thingSoC/TSOC_GROVEY_ONE/TSOC_GROVEY_ONE/documentation/pinout/TSOC_GROVEY_ONE_pinout.pdf

Sheet1

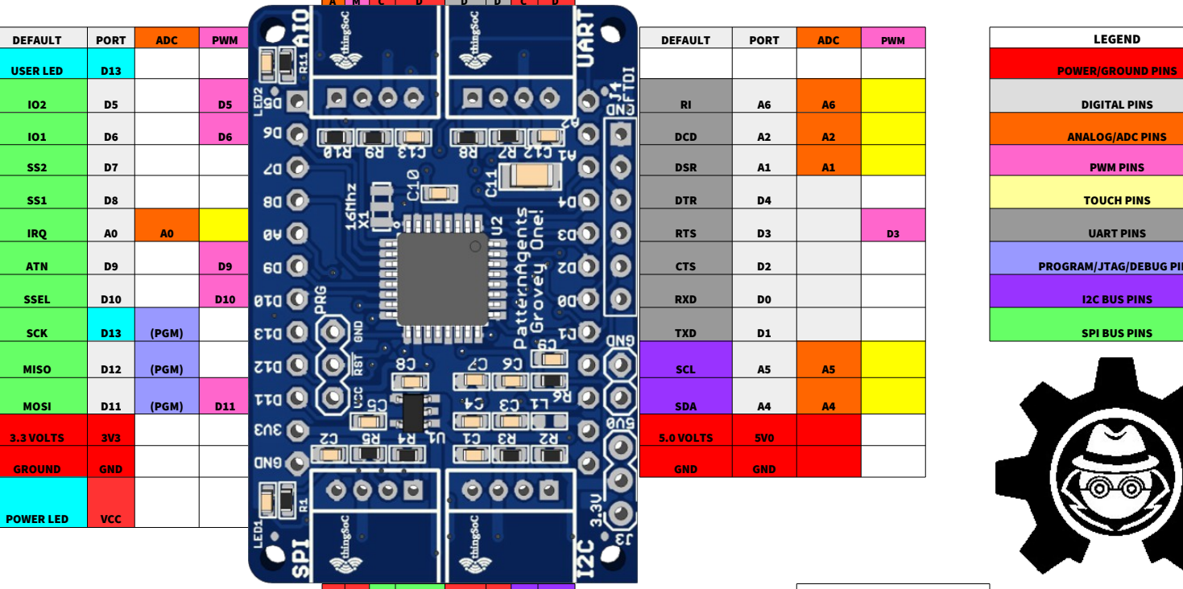
[picture p3: figure]
USER LED; POWER/GROUND PINS; DIGITAL PINS; DCD; ANALOG/ADC PINS; DSR; PWM PINS; DTR; TOUCH PINS; IRQ; RTS; UART PINS; SSEL; RXD; I2C BUS PINS; SCK; (PGM); TXD; SPI BUS PINS; MISO; SCL; MOSI; SDA; 3.3 VOLTS; 5.0 VOLTS; GROUND; GND; POWER LED; VCC

Page 1

DEFAULT | PORT | ADC | PWM | DEFAULT | PORT | ADC | PWM | LEGEND
ATN | D9 | D9 | CTS | D2 | PROGRAM/JTAG/DEBUG PINS

## PatternAgents

TSOC_GROVEY_ONE

A 3 | D 5 | P W R | G N D | D 0 | D 1 | P W R | G N D
A N A | P W M | V C C | G N D | R X D | T X D | V C C | G N D

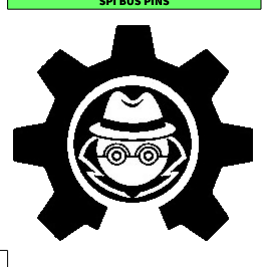
[picture p4: figure]

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
### 5 http://github.com/thingsoc/
