thingSoC/TSOC_GROVEY_ONE/TSOC_GROVEY_ONE/documentation/pinout/TSOC_GROVEY_ONE_pinout.jpg

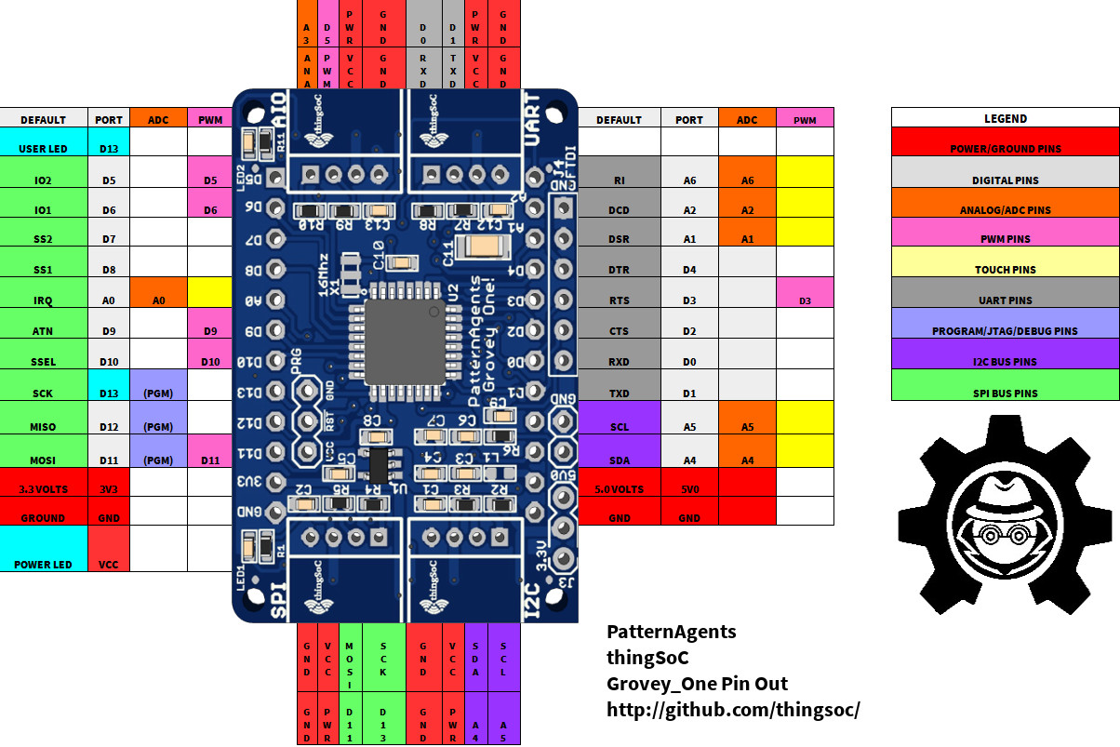
TSOC_GROVEY_ONE/documentation/pinout/TSOC_GROVEY_ONE_pinout.jpg
