thingSoC/TSOC_GROVEY_ONE/TSOC_GROVEY_ONE/eagleUp/eagleUp_TSOC_GROVEY_ONE_board_bottom.jpg

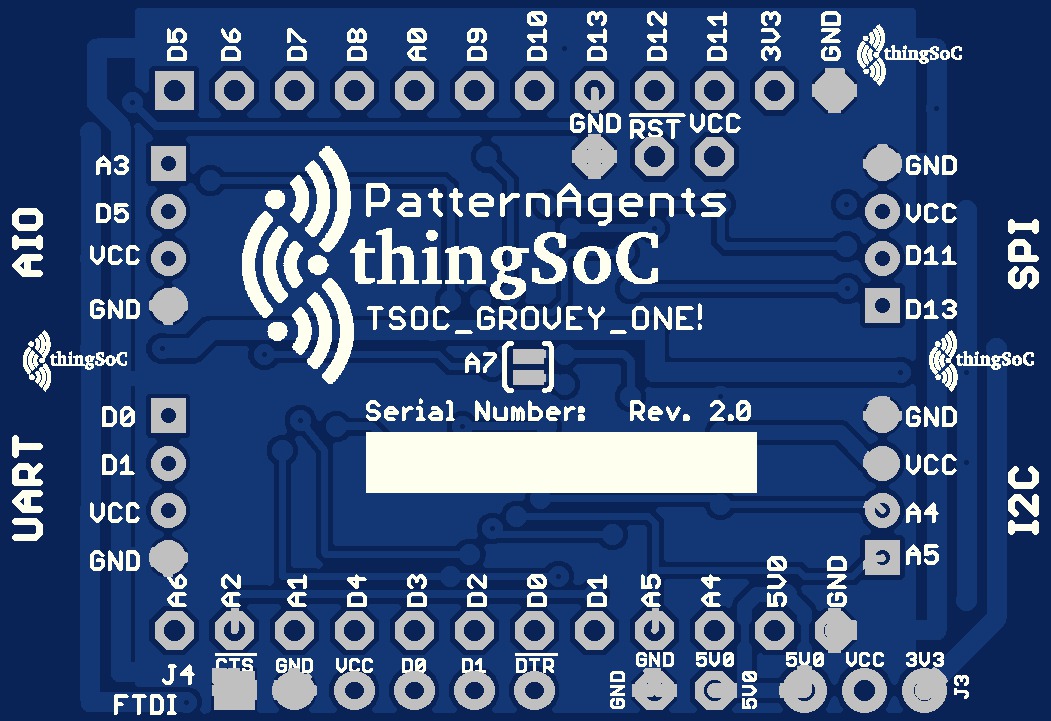
TSOC_GROVEY_ONE/eagleUp/eagleUp_TSOC_GROVEY_ONE_board_bottom.jpg
