thingSoC/TSOC_GROVEY_ONE/TSOC_GROVEY_ONE/images/product/TSOC_GROVEY_ONE_pop_top.png

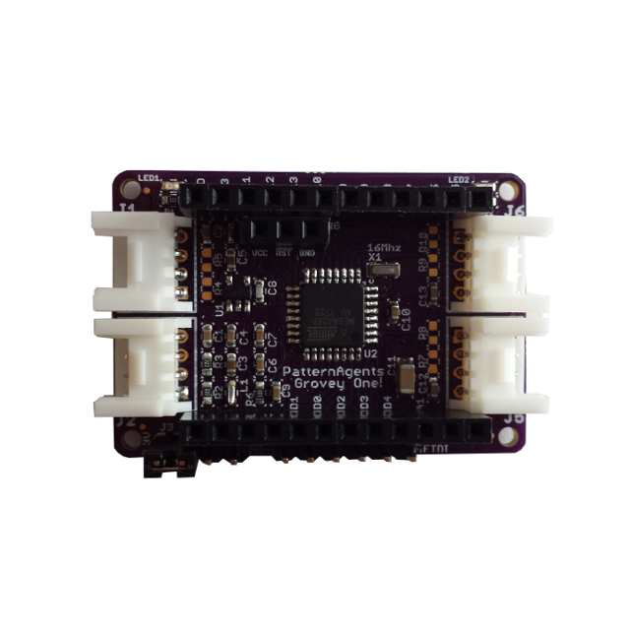
TSOC_GROVEY_ONE/images/product/TSOC_GROVEY_ONE_pop_top.png
