thingSoC/TSOC_GROVEY_ONE/TSOC_GROVEY_ONE/images/product/TSOC_GROVEY_ONE_top_pop.png

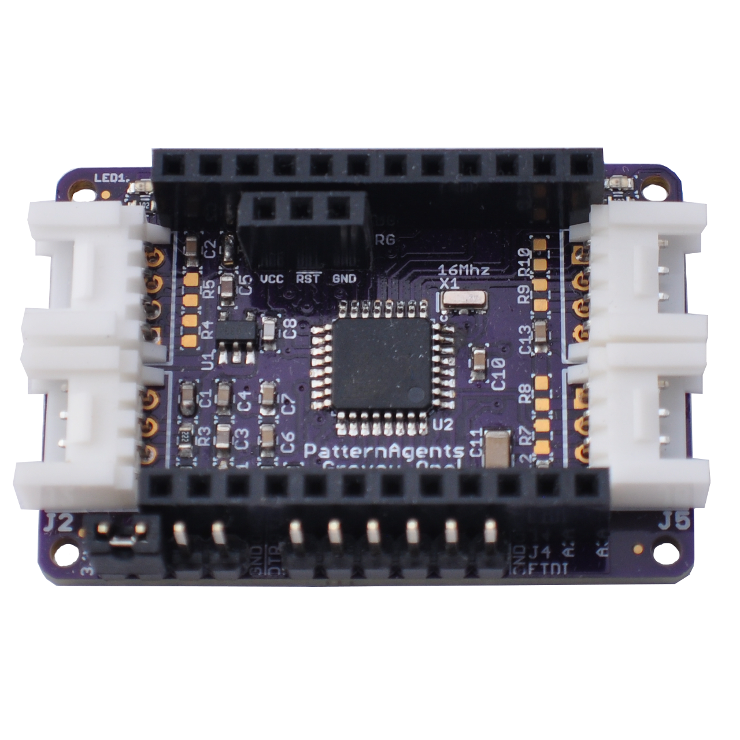
TSOC_GROVEY_ONE/images/product/TSOC_GROVEY_ONE_top_pop.png
