thingSoC/TSOC_GROVEY_ONE/TSOC_GROVEY_ONE/images/product/TSOC_GROVEY_ONE_with_FTDI_long.jpg

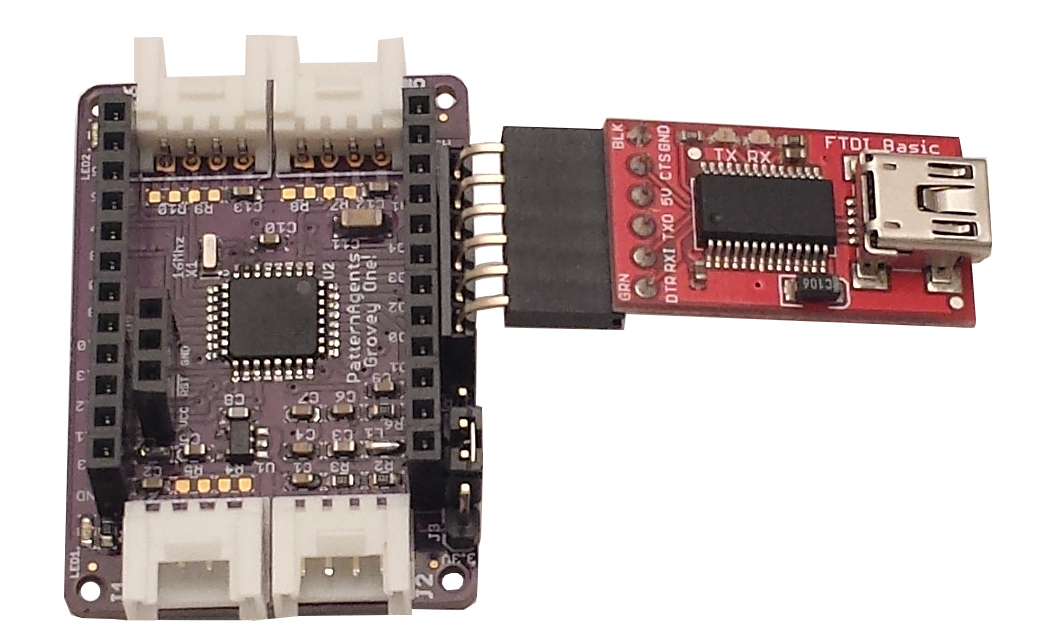
TSOC_GROVEY_ONE/images/product/TSOC_GROVEY_ONE_with_FTDI_long.jpg
