thingSoC/TSOC_GROVEY_ONE/TSOC_GROVEY_ONE/images/product/TSOC_GROVEY_ONE_with_programmer.jpg

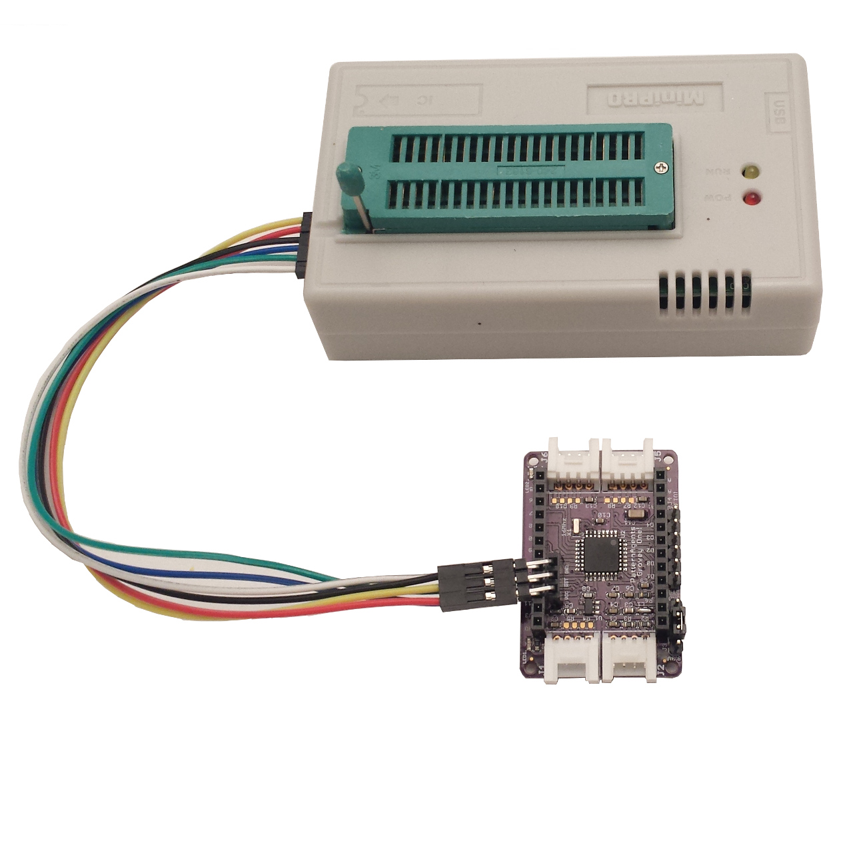
TSOC_GROVEY_ONE/images/product/TSOC_GROVEY_ONE_with_programmer.jpg
