thingSoC/TSOC_GROVEY_ONE/TSOC_GROVEY_ONE/images/raw/20160921_100233.jpg

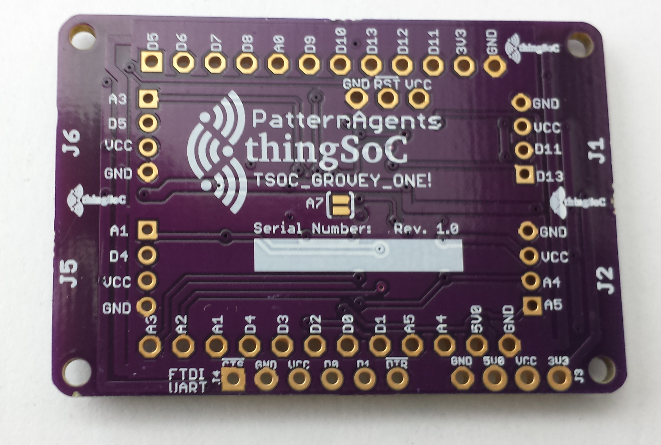
TSOC_GROVEY_ONE/images/raw/20160921_100233.jpg
