thingSoC/TSOC_GROVEY_ONE/TSOC_GROVEY_ONE/images/raw/20160928_184255.jpg

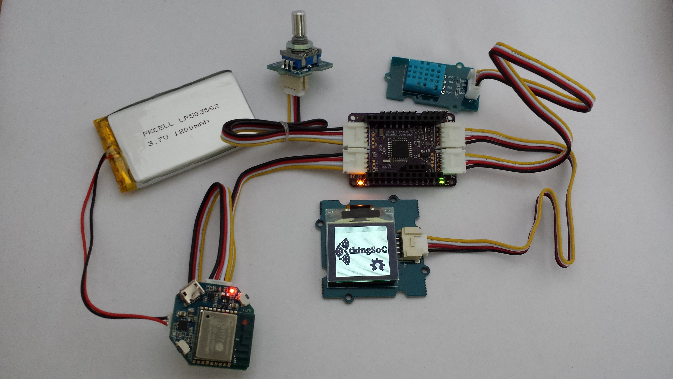
TSOC_GROVEY_ONE/images/raw/20160928_184255.jpg
