thingSoC/TSOC_GROVEY_ONE/TSOC_GROVEY_ONE/images/raw/20160929_131808.jpg

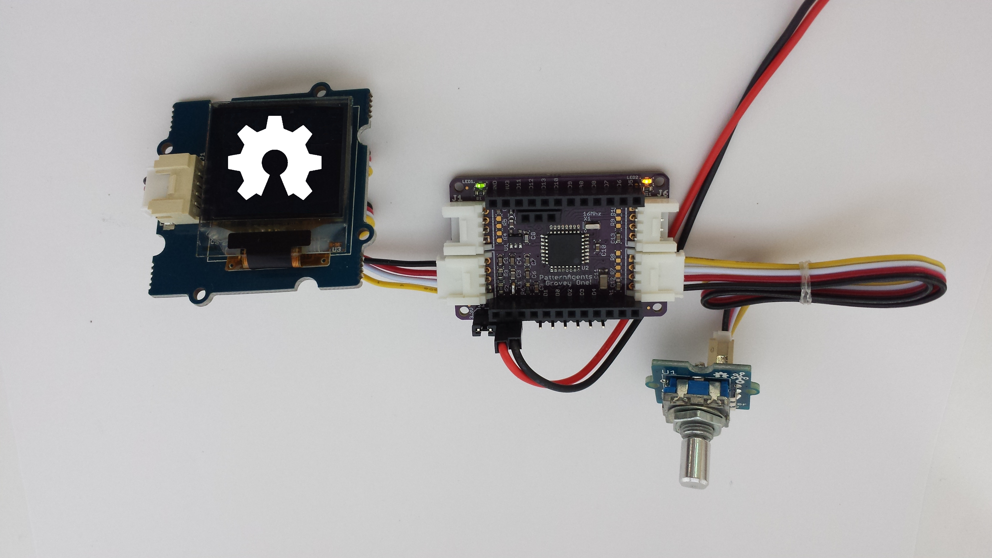
TSOC_GROVEY_ONE/images/raw/20160929_131808.jpg
