thingSoC/TSOC_GROVEY_ONE/TSOC_GROVEY_ONE/images/raw/20160929_132144.jpg

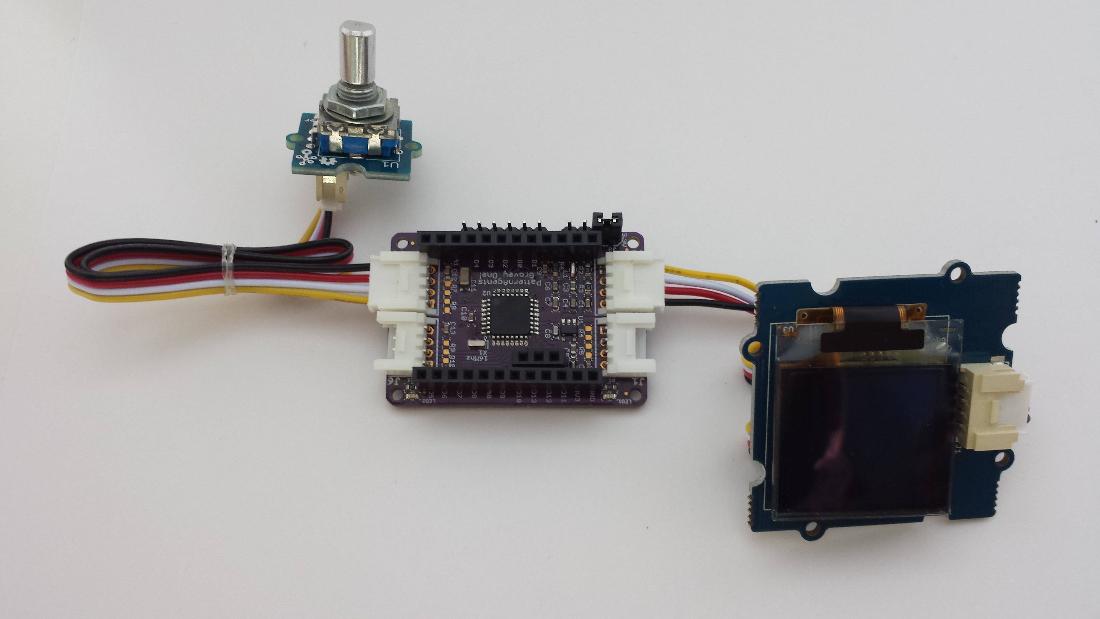
TSOC_GROVEY_ONE/images/raw/20160929_132144.jpg
