thingSoC/TSOC_GROVEY_ONE/TSOC_GROVEY_ONE/revisions/R1_0/TSOC_GROVEY_ONE_iso.png

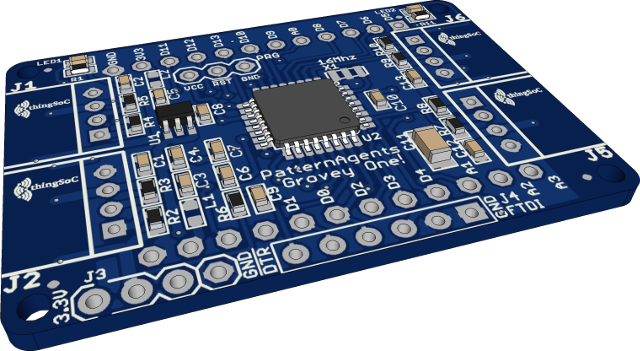
TSOC_GROVEY_ONE/revisions/R1_0/TSOC_GROVEY_ONE_iso.png
