thingSoC/TSOC_GROVEY_ONE/TSOC_GROVEY_ONE/revisions/R1_0/TSOC_GROVEY_ONE_top.png

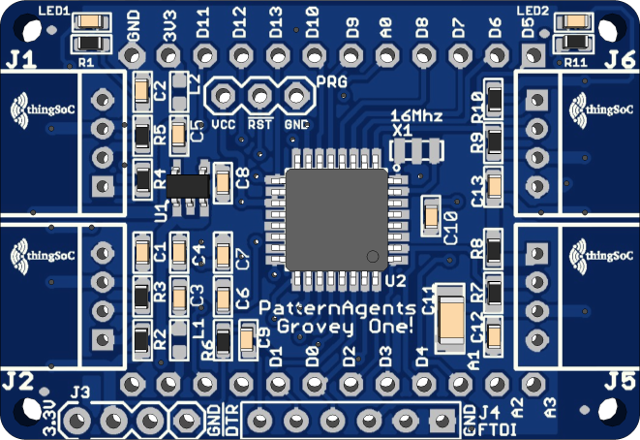
TSOC_GROVEY_ONE/revisions/R1_0/TSOC_GROVEY_ONE_top.png
