thingSoC/TSOC_GROVEY_ONE/TSOC_GROVEY_ONE/hardware/TSOC_GROVEY_ONE_sch.pdf

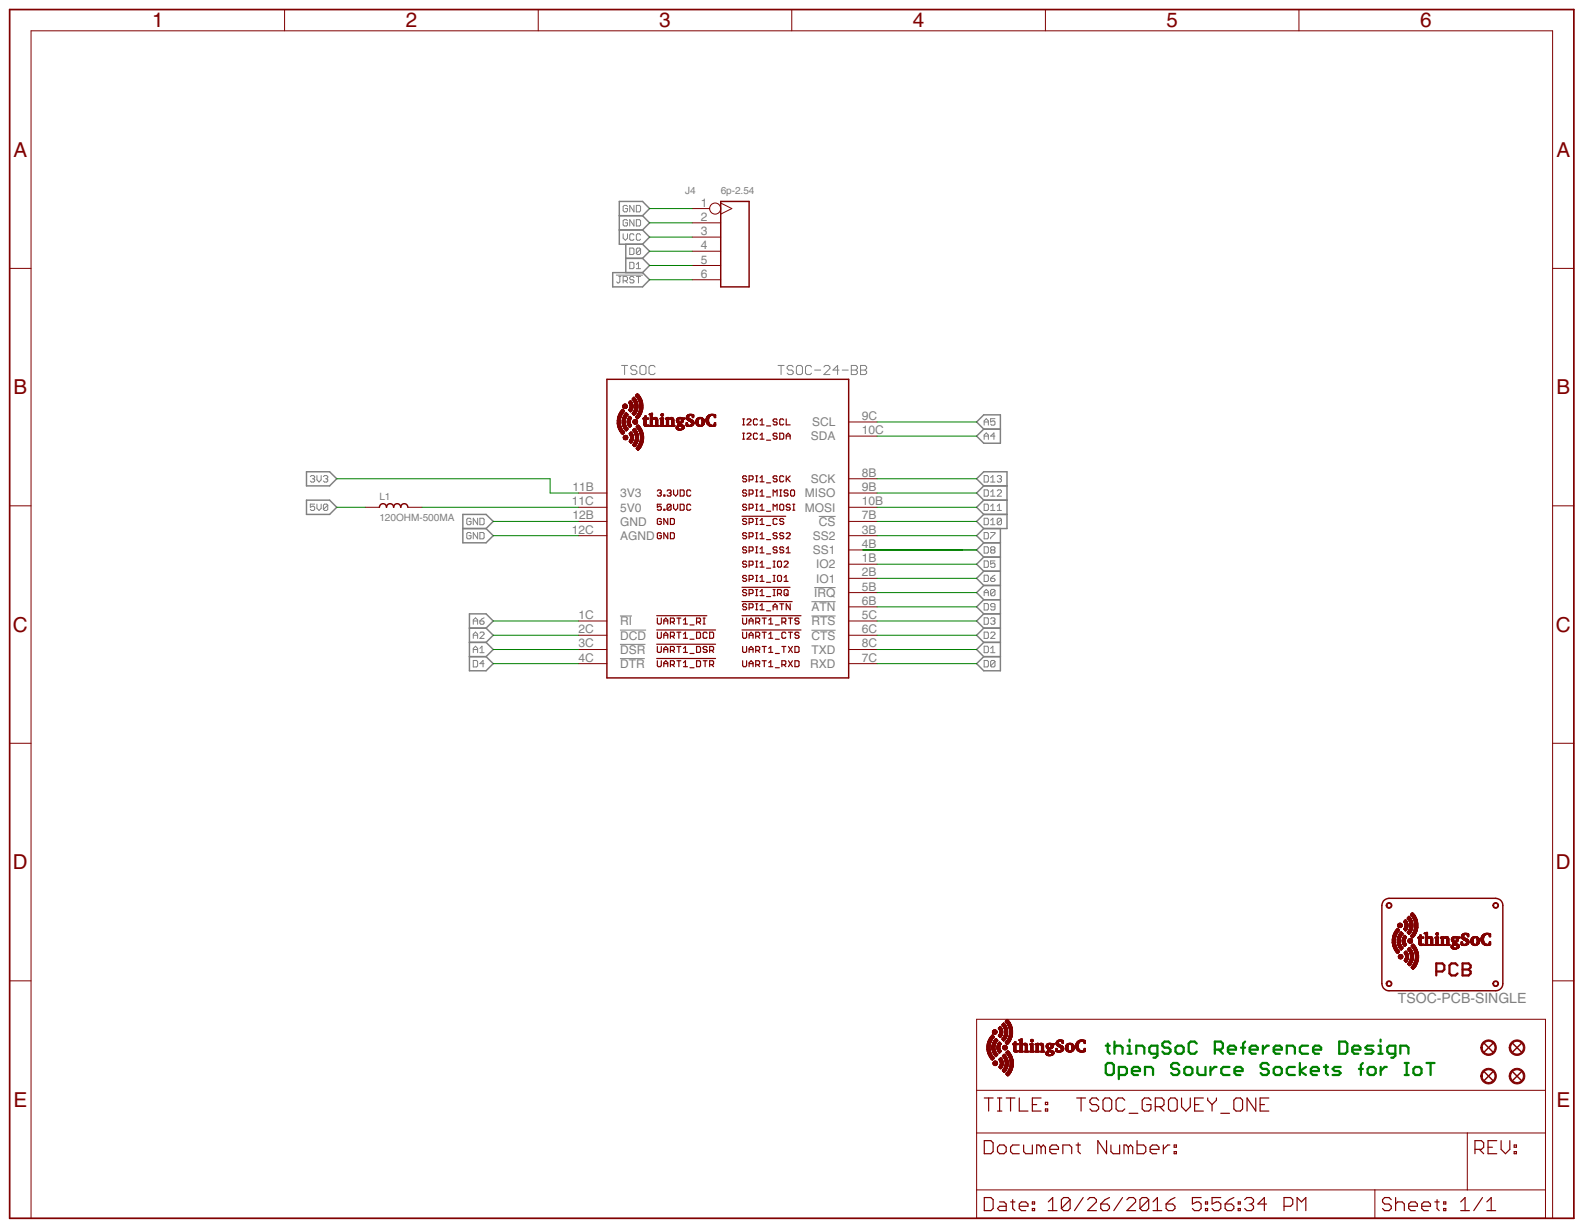
[picture p48: page 1]

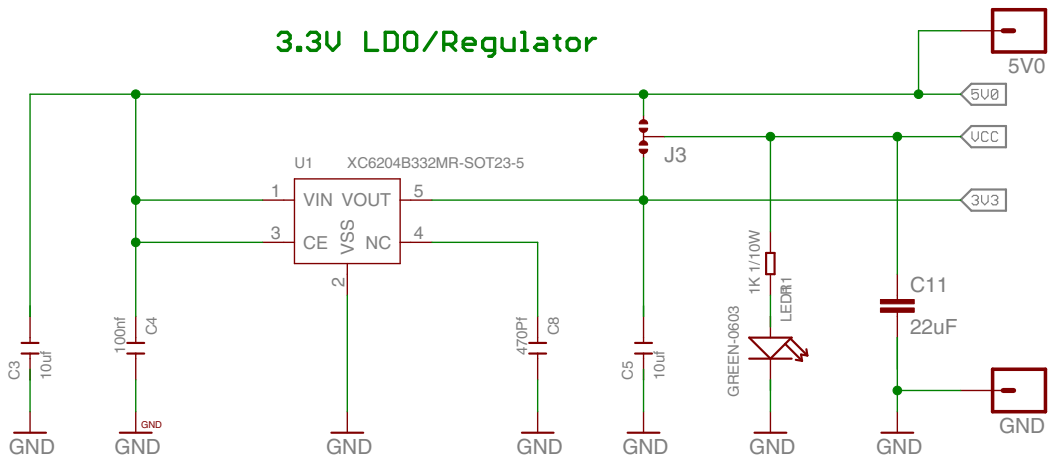
[picture p49: page 2]

100nf GND GND GND GND

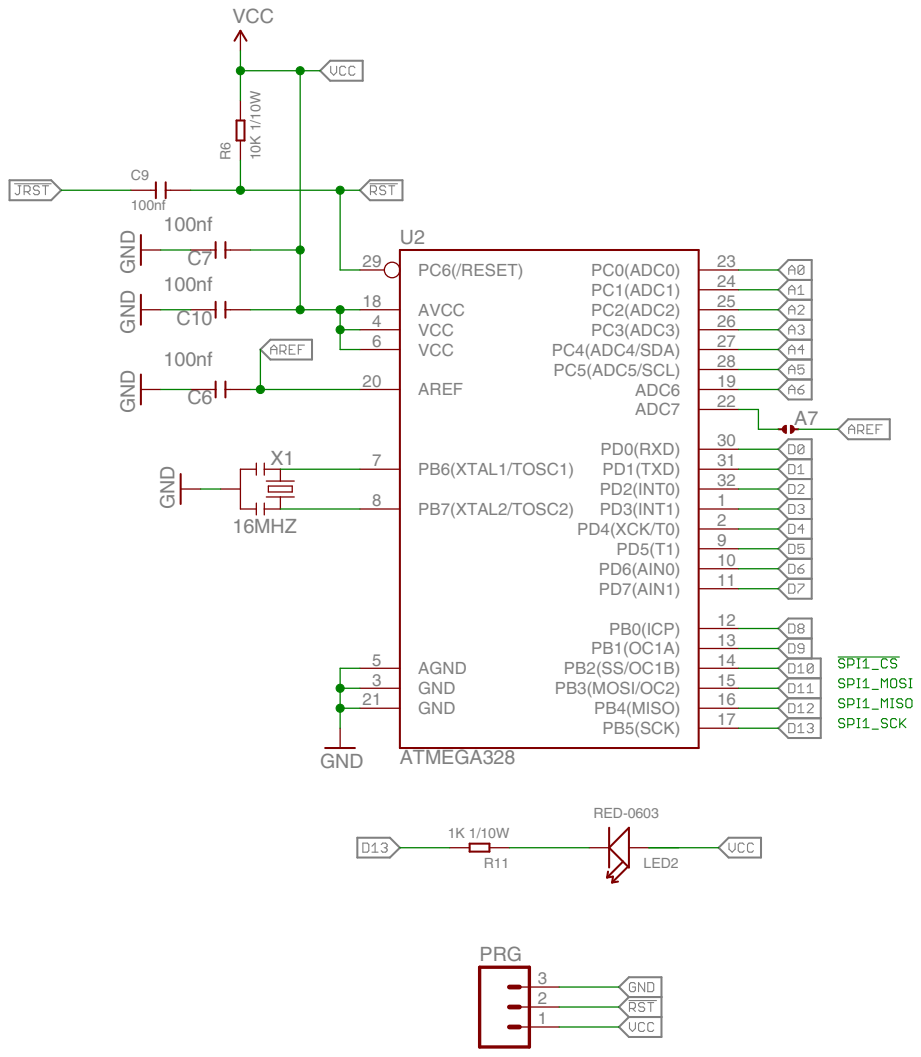
[picture p50: page 3]

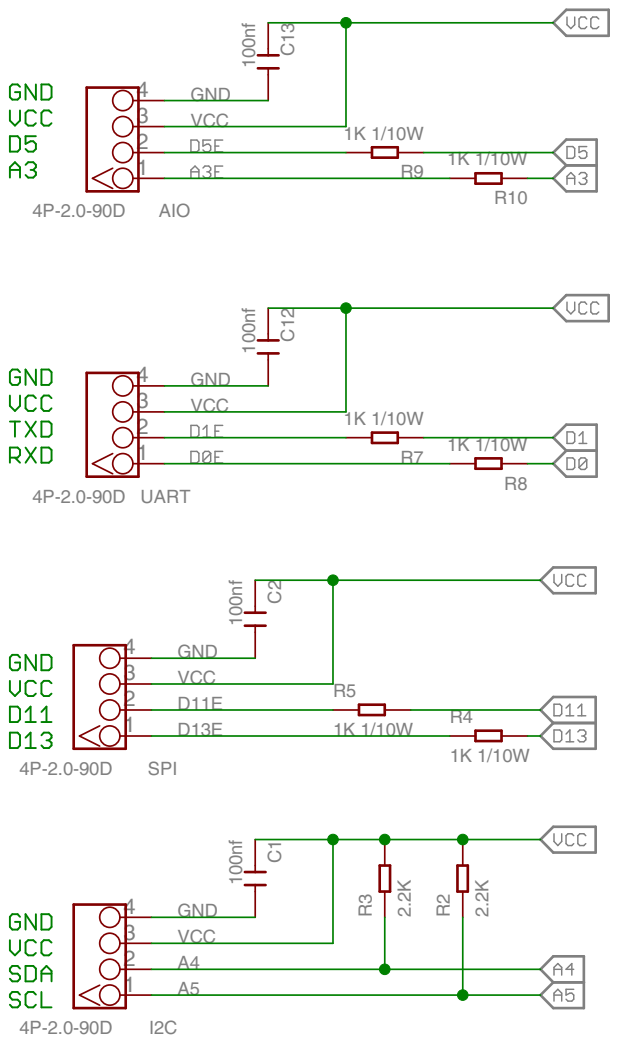
[picture p51: page 4]
