thingSoC/TSOC_GROVEY_ONE/TSOC_GROVEY_ONE/hardware/TSOC_GROVEY_ONE_sch_black.pdf

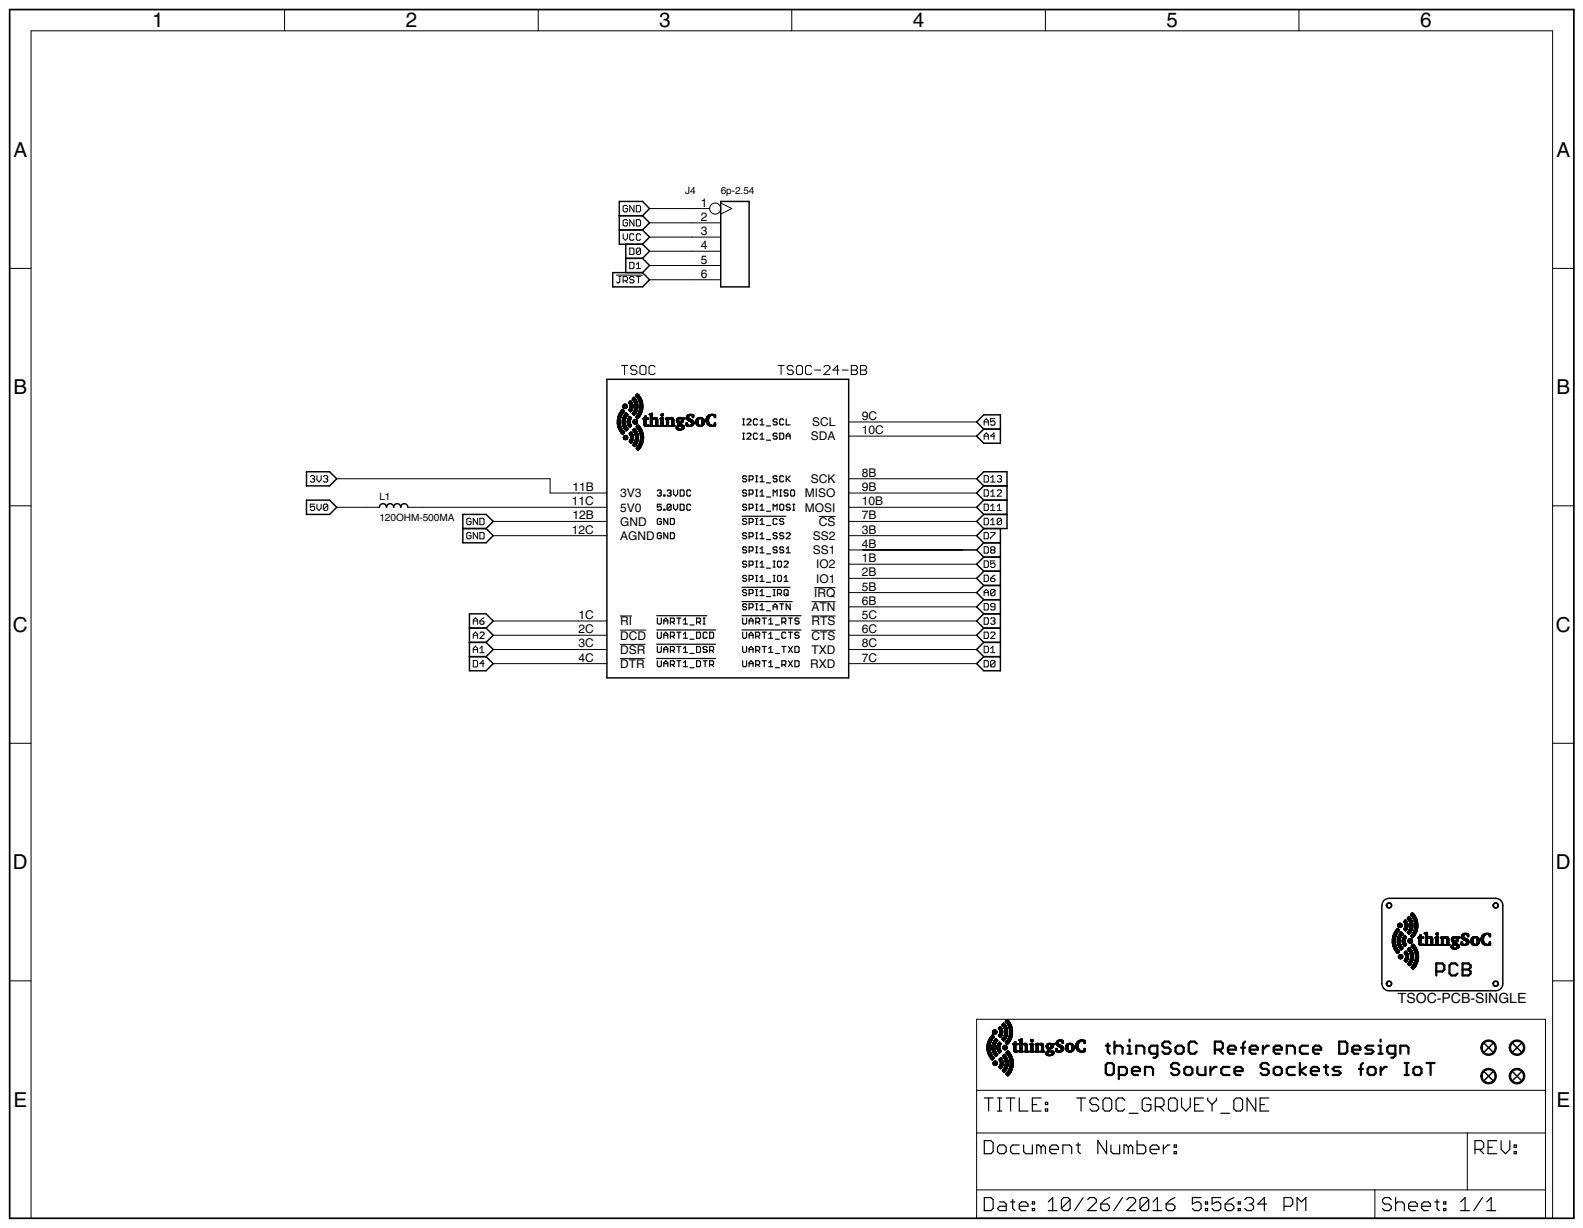
[picture p52: page 1]

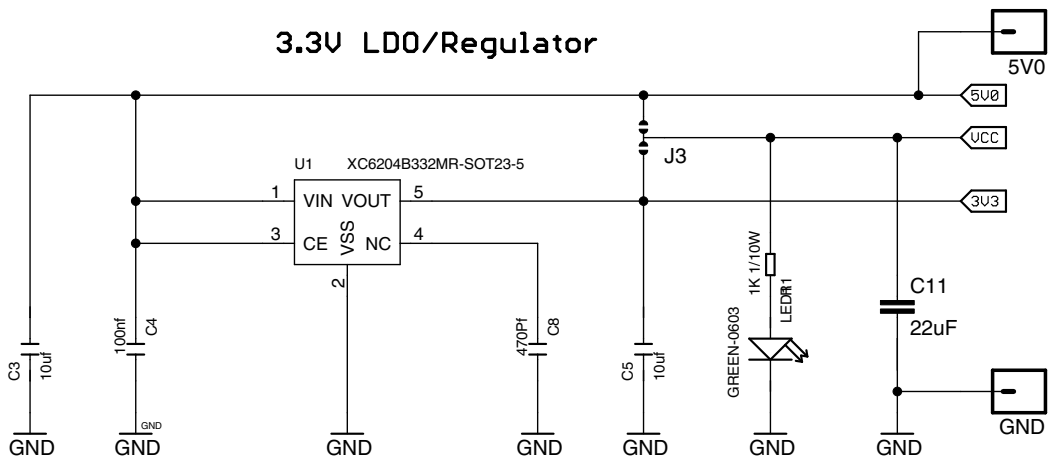
[picture p53: page 2]

100nf GND GND GND GND

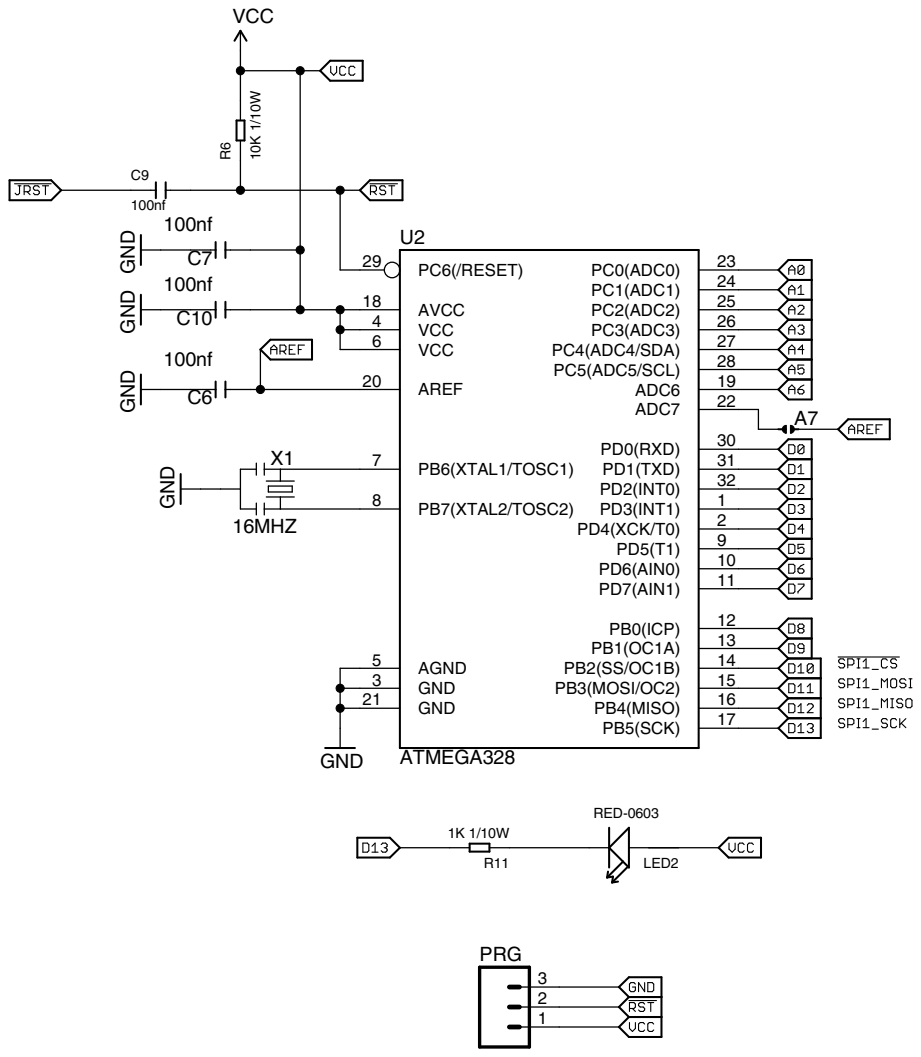
[picture p54: page 3]

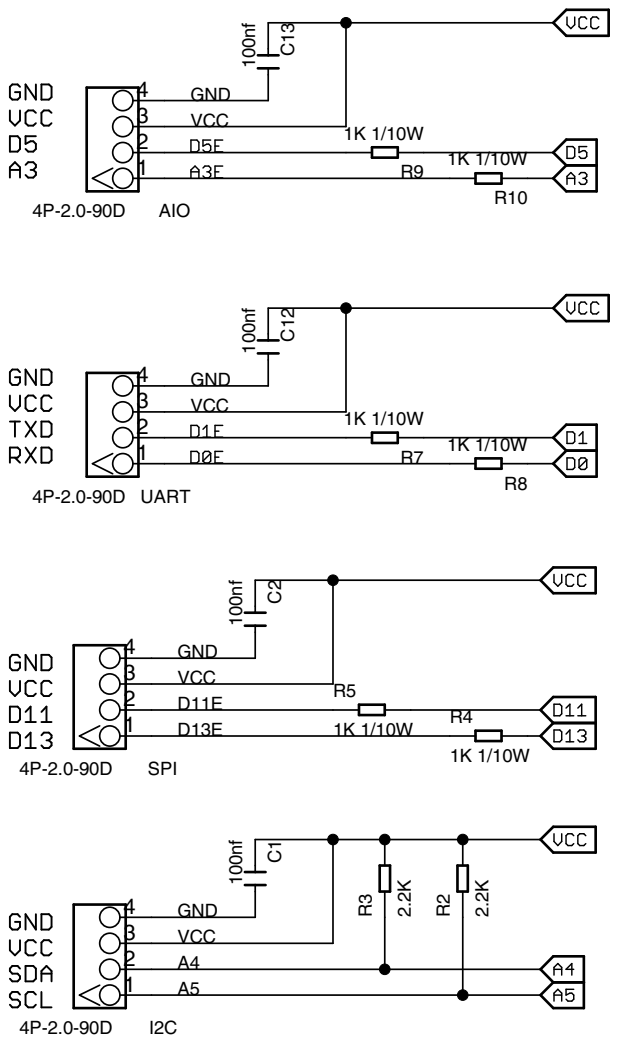
[picture p55: page 4]
