thingSoC/TSOC_GROVEY_ONE/TSOC_GROVEY_ONE/hardware/TSOC_GROVEY_ONE_bsilk.pdf

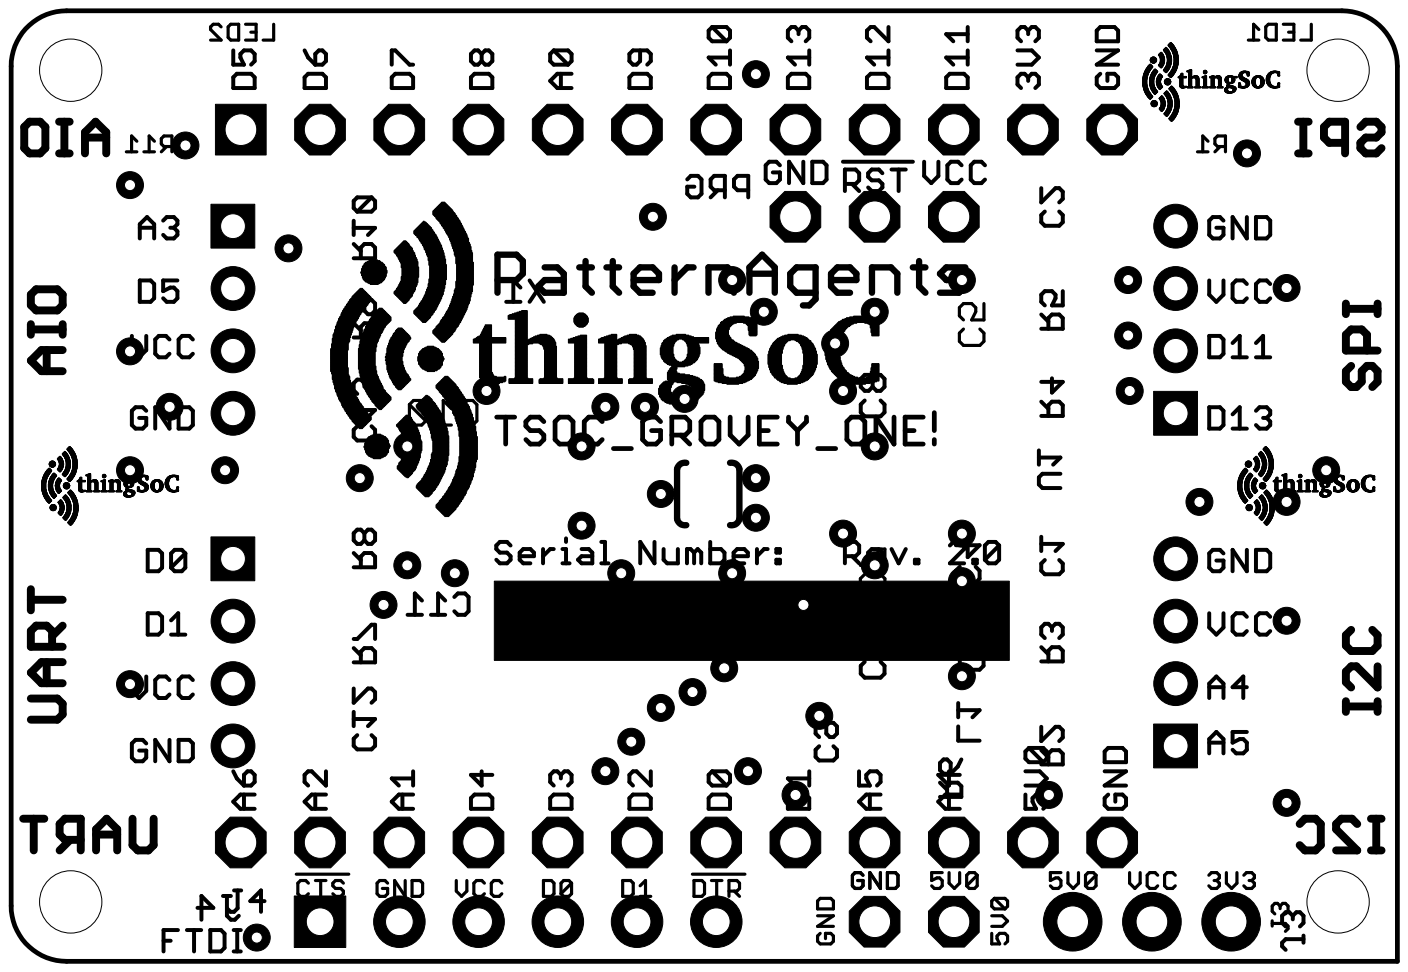
[picture p63: page 1]
