thingSoC/TSOC_GROVEY_ONE/TSOC_GROVEY_ONE/hardware/TSOC_GROVEY_ONE_tsilk.pdf

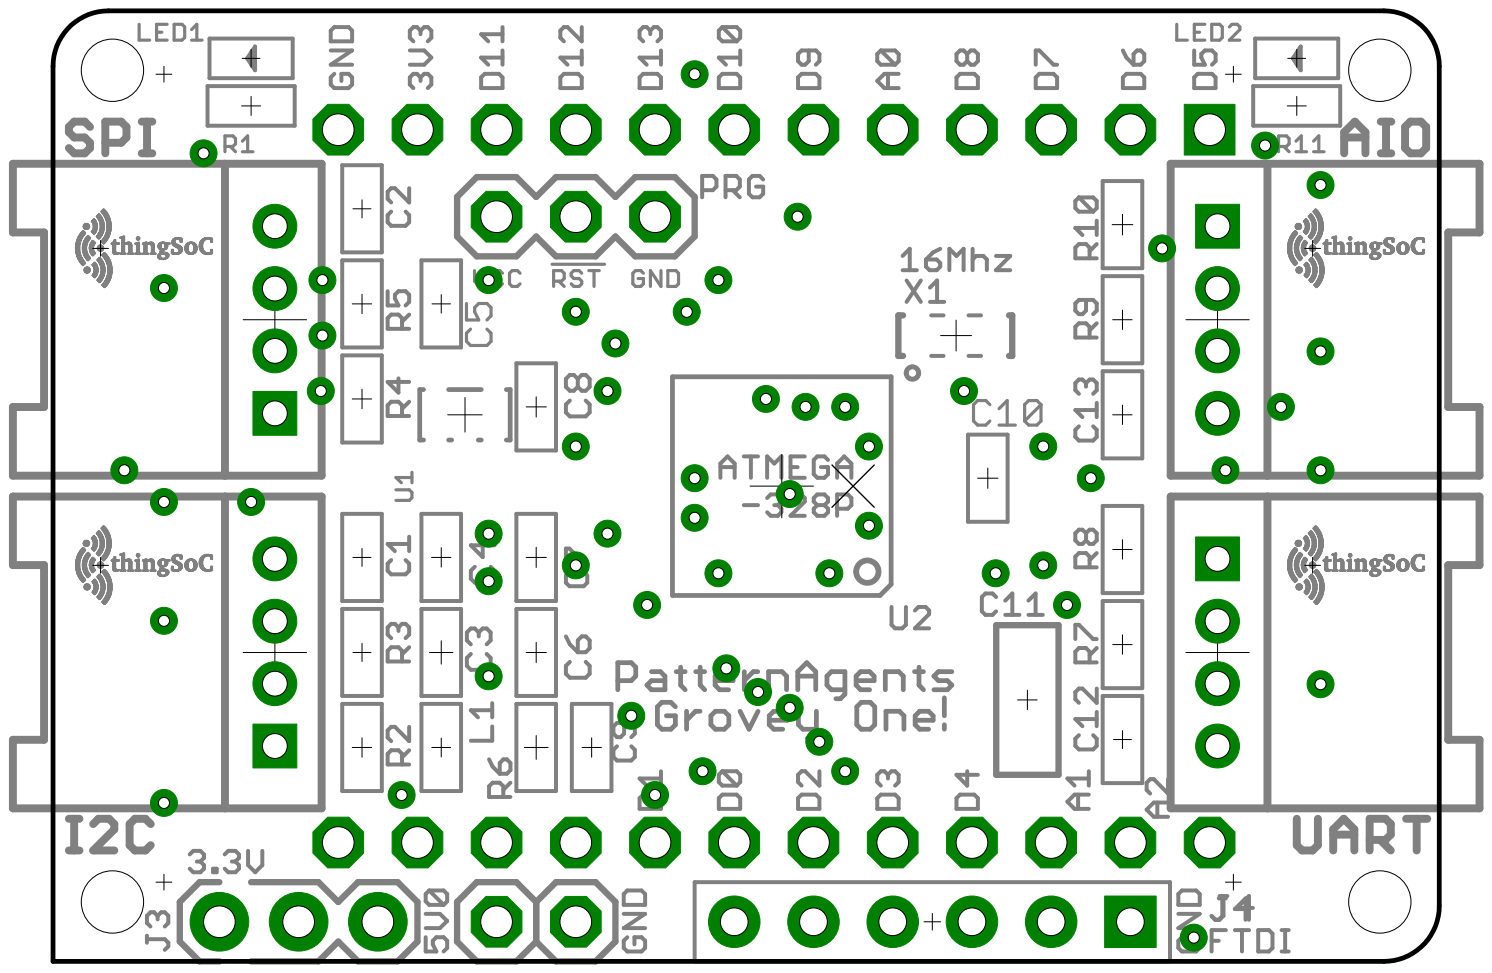
[picture p64: page 1]
